emrsmsrli/WordClock/etc/img/backplate/1.jpg

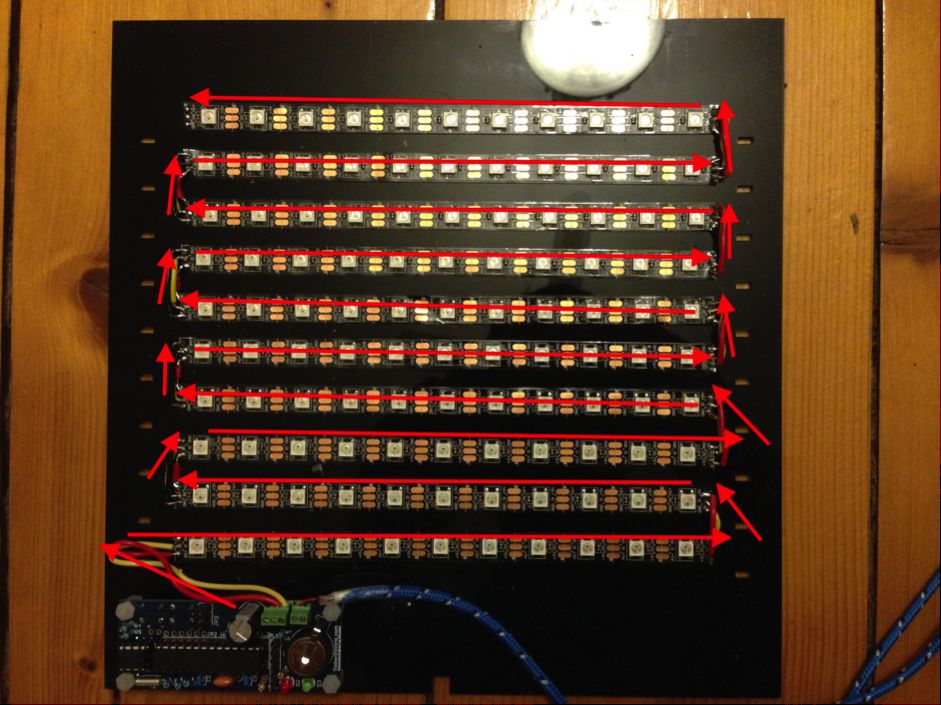
etc/img/backplate/1.jpg
