emrsmsrli/WordClock/etc/img/backplate/2.jpg

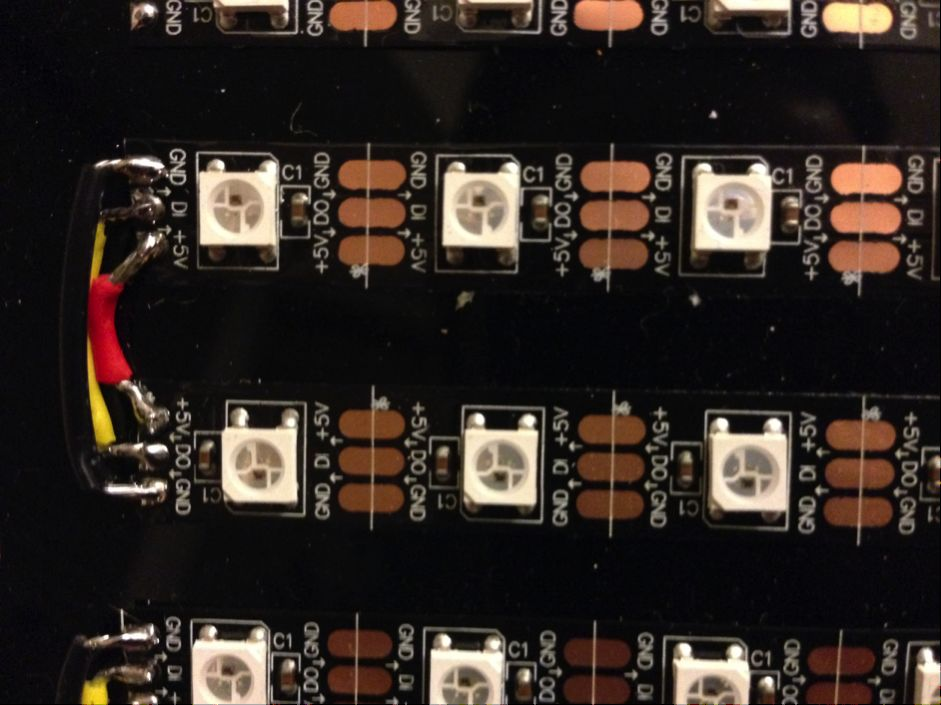
etc/img/backplate/2.jpg
