emrsmsrli/WordClock/etc/img/backplate/3.jpg

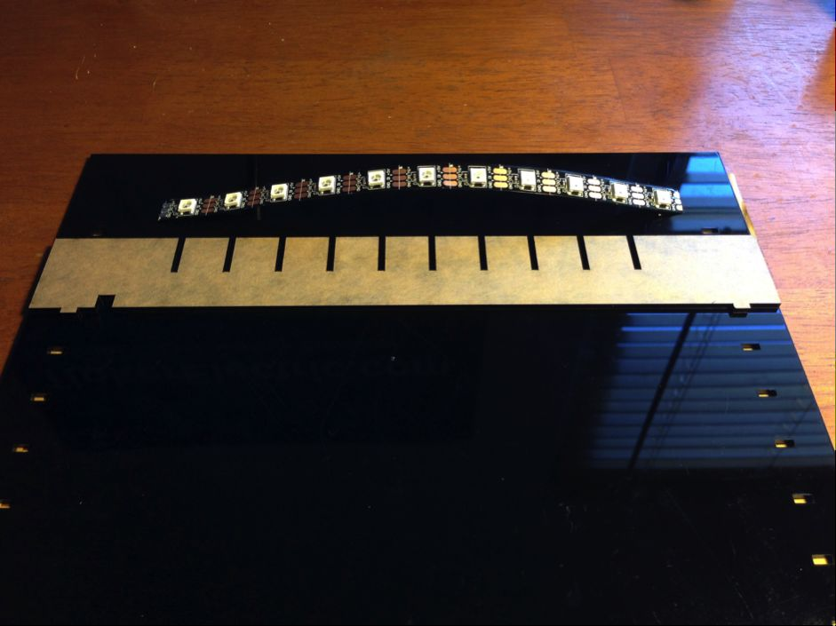
etc/img/backplate/3.jpg
