emrsmsrli/WordClock/etc/img/backplate/4.jpg

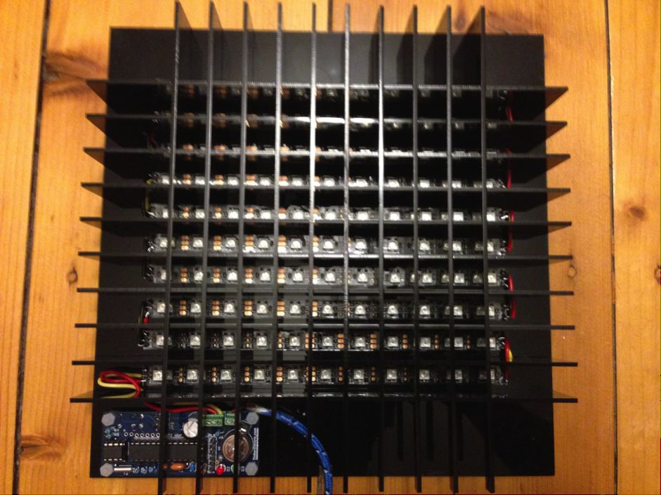
etc/img/backplate/4.jpg
