emrsmsrli/WordClock/etc/img/backplate/5.jpg

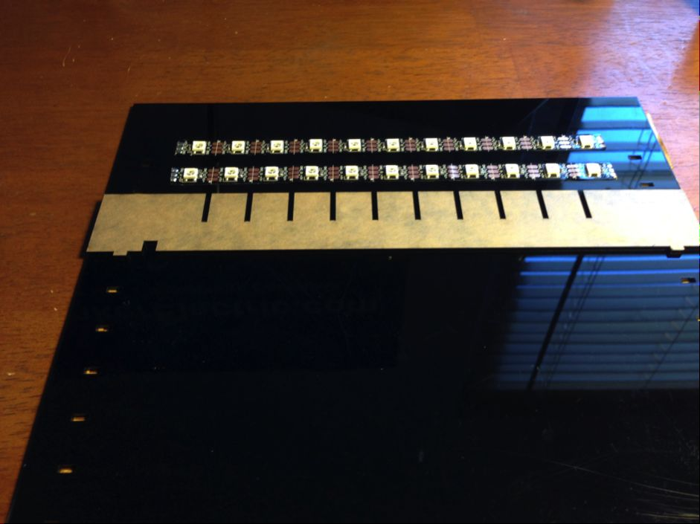
etc/img/backplate/5.jpg
