emrsmsrli/WordClock/etc/img/backplate/6.jpg

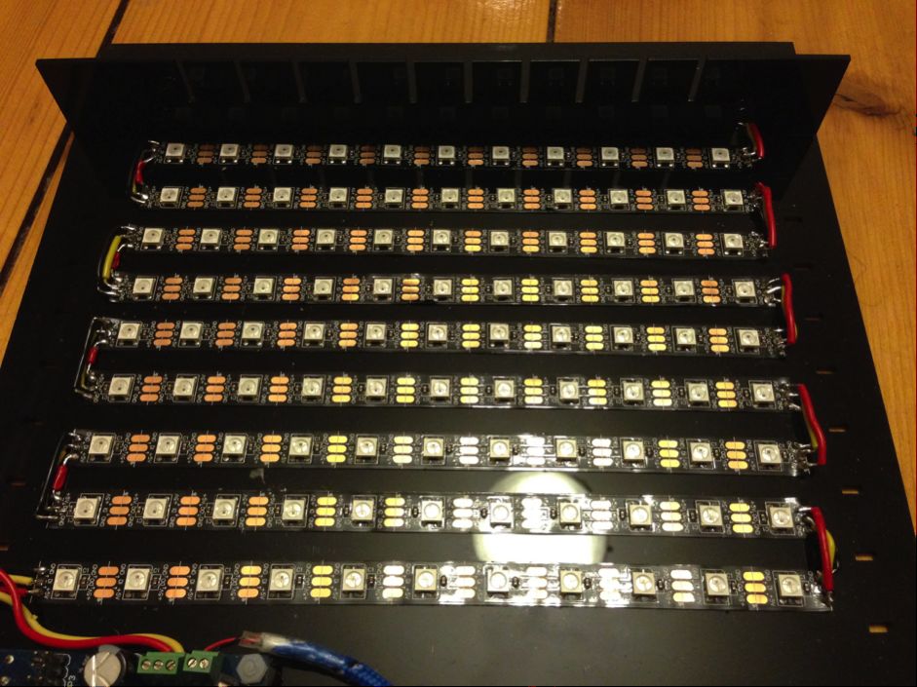
etc/img/backplate/6.jpg
