emrsmsrli/WordClock/etc/img/backplate/7.jpg

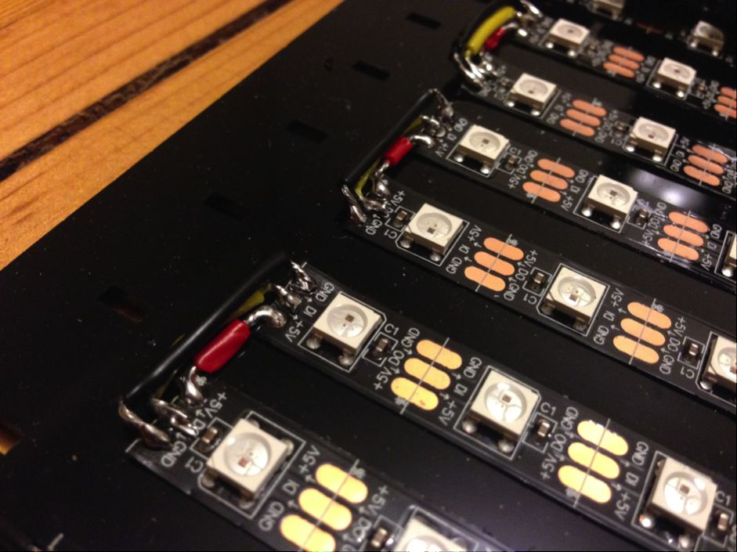
etc/img/backplate/7.jpg
