emrsmsrli/WordClock/etc/img/backplate/8.jpg

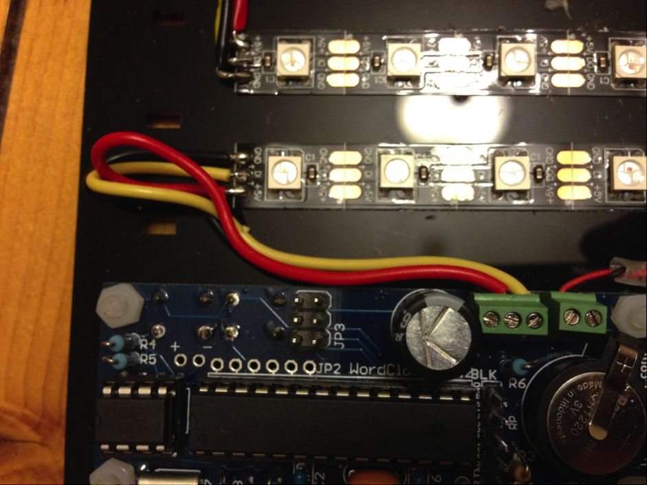
etc/img/backplate/8.jpg
