emrsmsrli/WordClock/etc/img/backplate/9.jpg

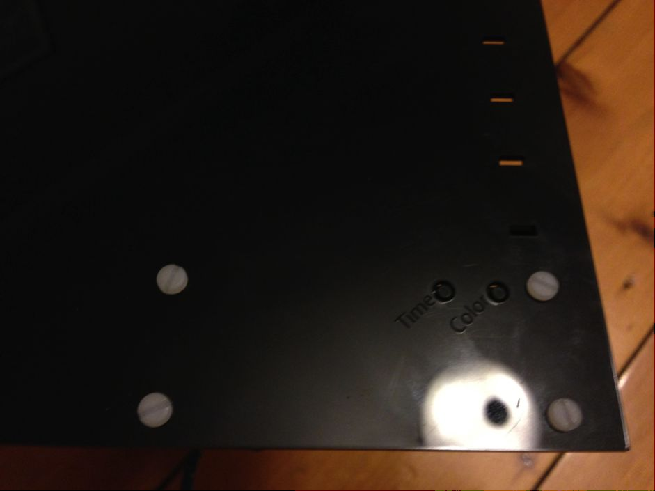
etc/img/backplate/9.jpg
