emrsmsrli/WordClock/etc/img/backplate/10.jpg

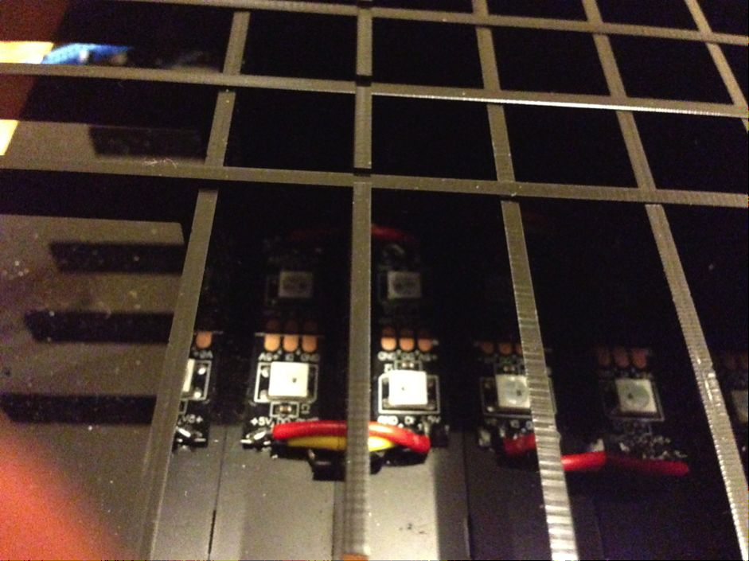
etc/img/backplate/10.jpg
