emrsmsrli/WordClock/etc/img/backplate/11.jpg

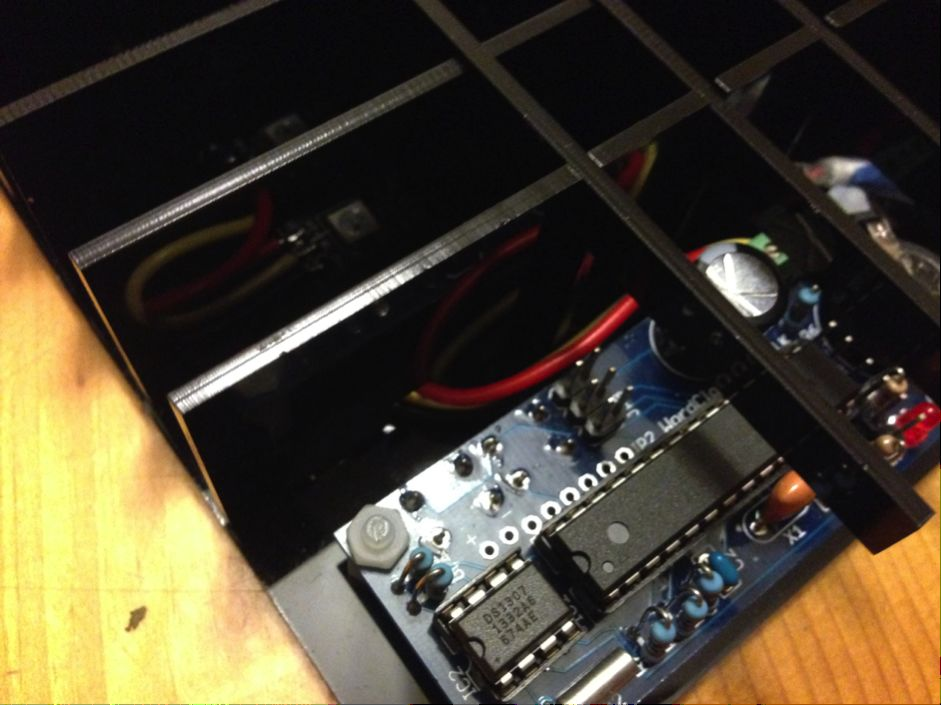
etc/img/backplate/11.jpg
