emrsmsrli/WordClock/etc/img/backplate/12.jpg

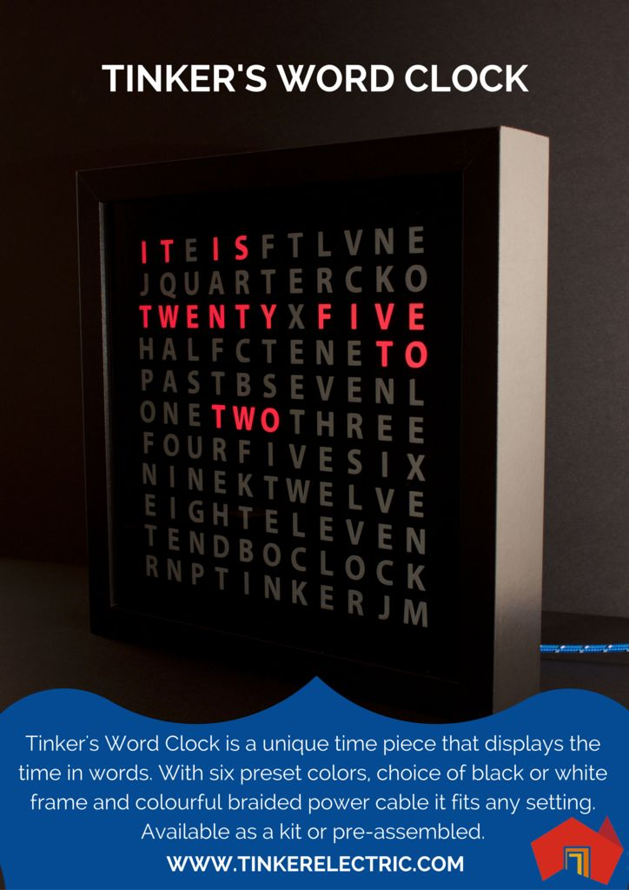
etc/img/backplate/12.jpg
