emrsmsrli/WordClock/etc/img/circuit/4.jpg

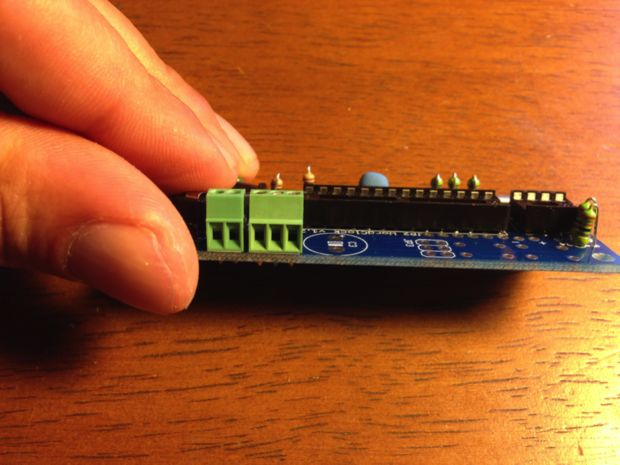
etc/img/circuit/4.jpg
