emrsmsrli/WordClock/etc/img/circuit/5.jpg

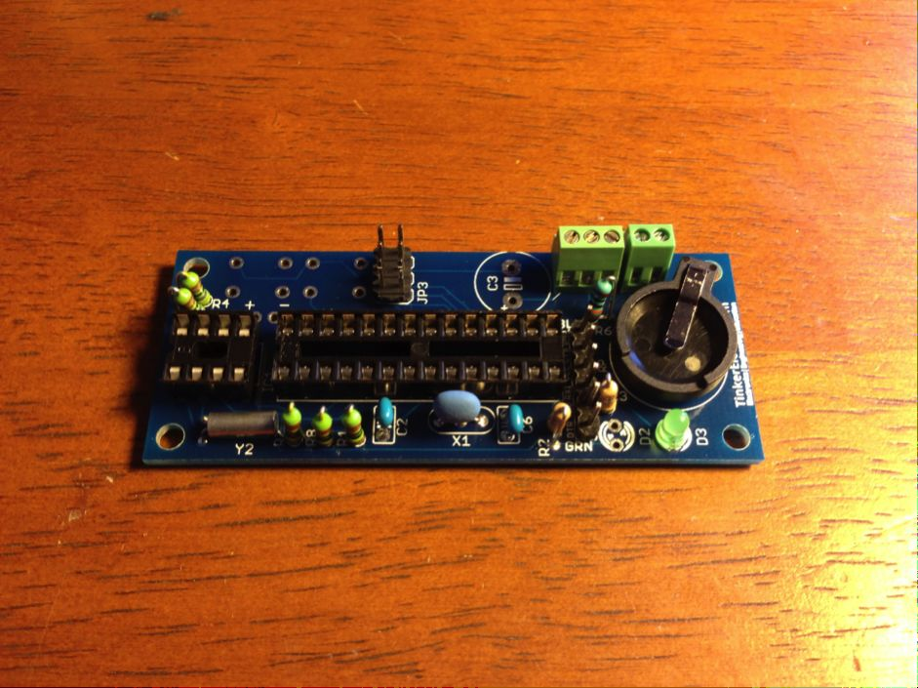
etc/img/circuit/5.jpg
