emrsmsrli/WordClock/etc/img/circuit/6.jpg

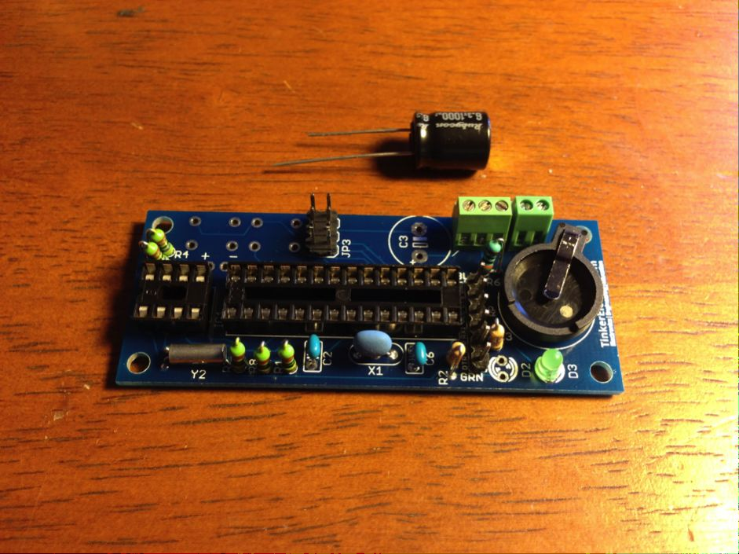
etc/img/circuit/6.jpg
