emrsmsrli/WordClock/etc/img/circuit/7.jpg

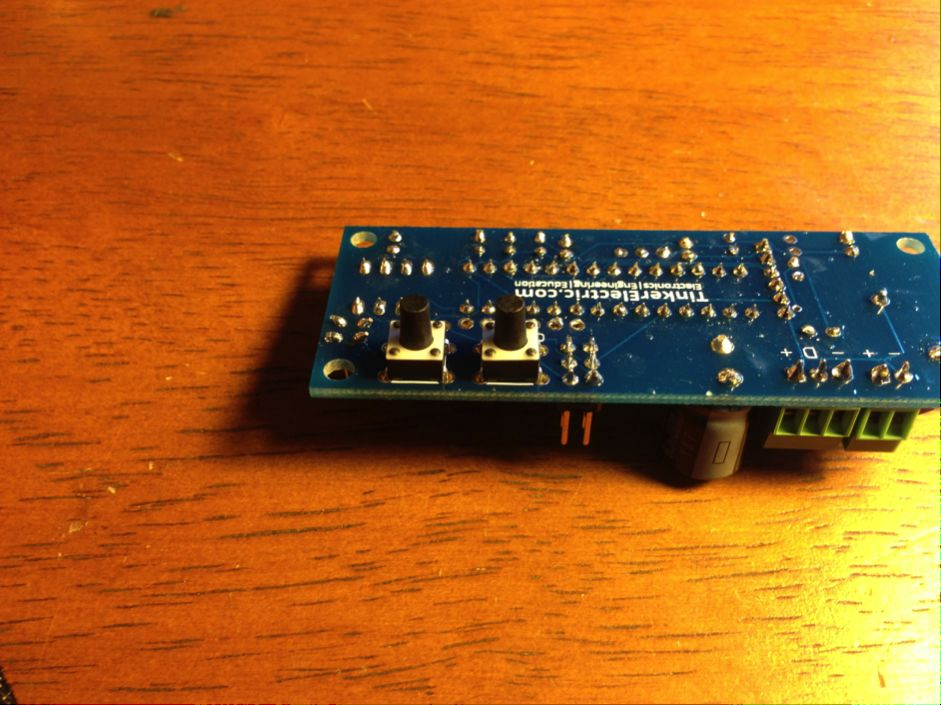
etc/img/circuit/7.jpg
