emrsmsrli/WordClock/etc/img/circuit/8.jpg

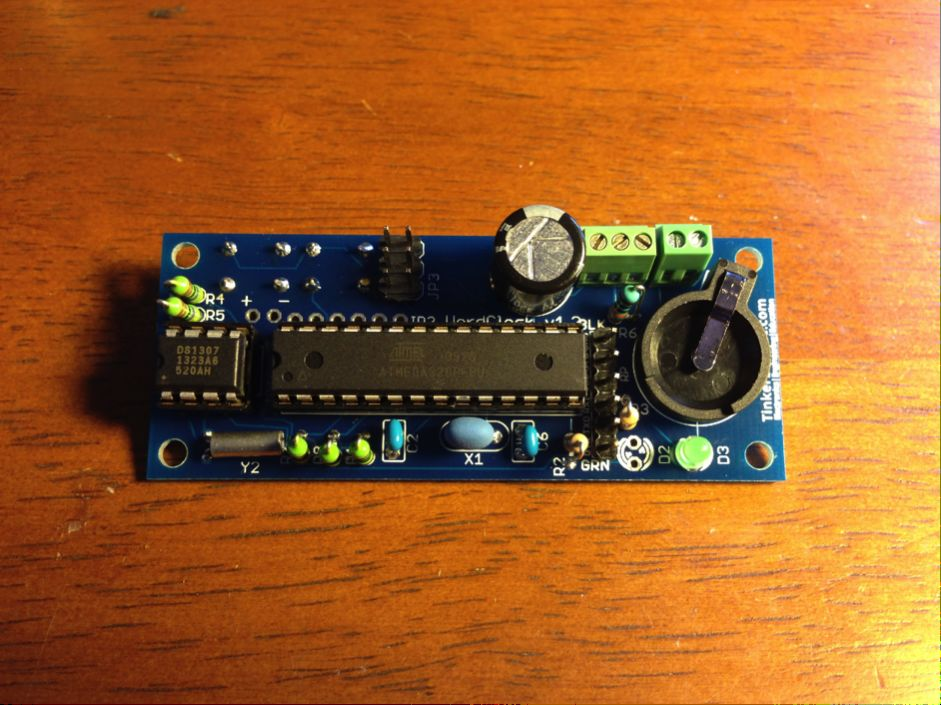
etc/img/circuit/8.jpg
