emrsmsrli/WordClock/etc/img/circuit/9.jpg

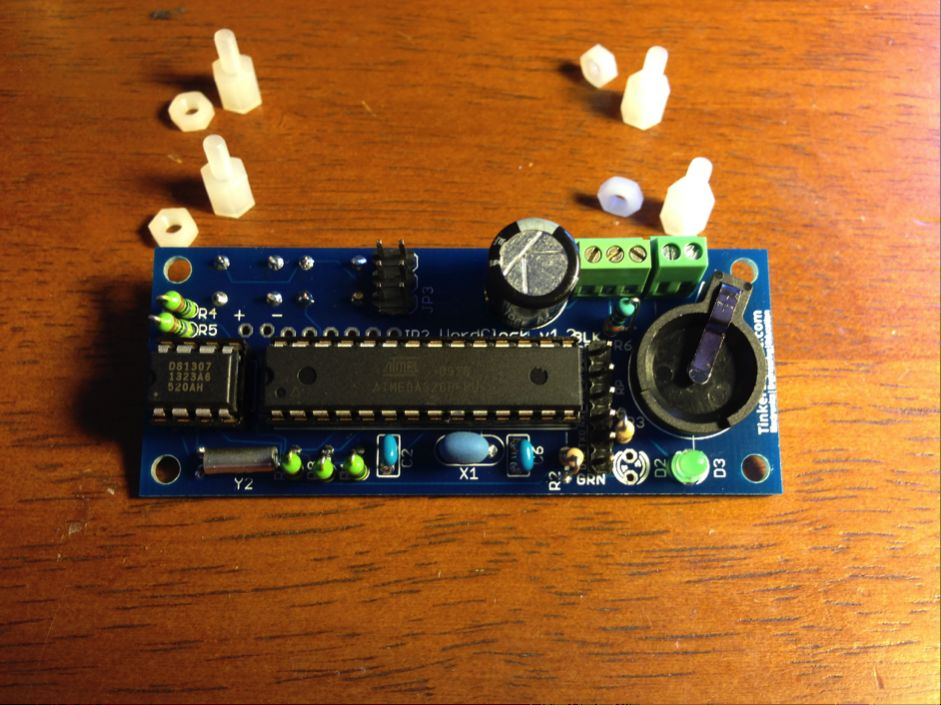
etc/img/circuit/9.jpg
