emrsmsrli/WordClock/etc/img/circuit/10.jpg

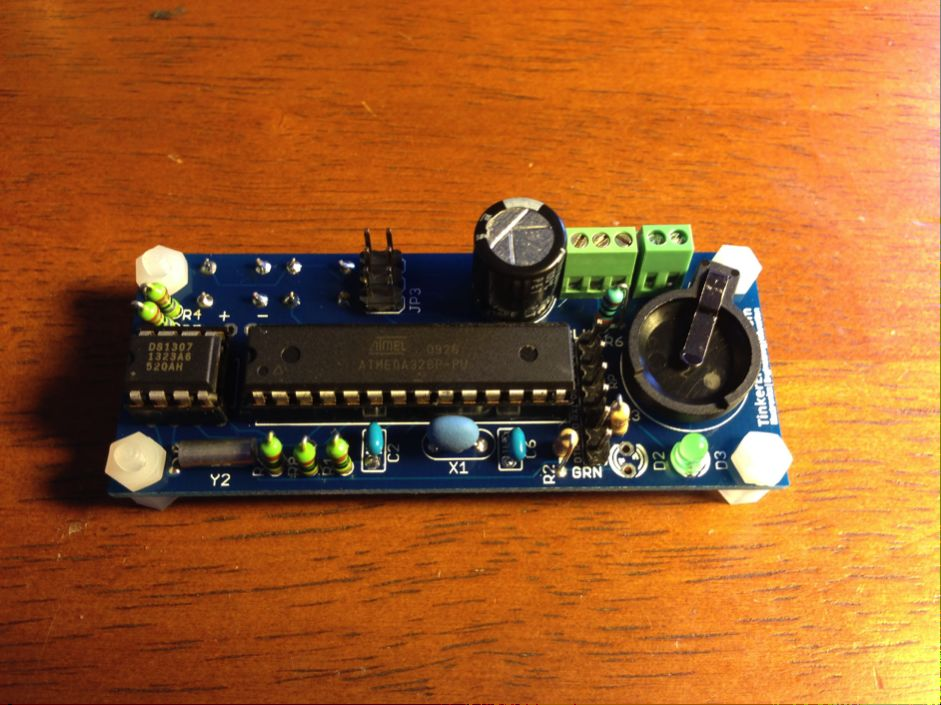
etc/img/circuit/10.jpg
