emrsmsrli/WordClock/etc/img/circuit/11.jpg

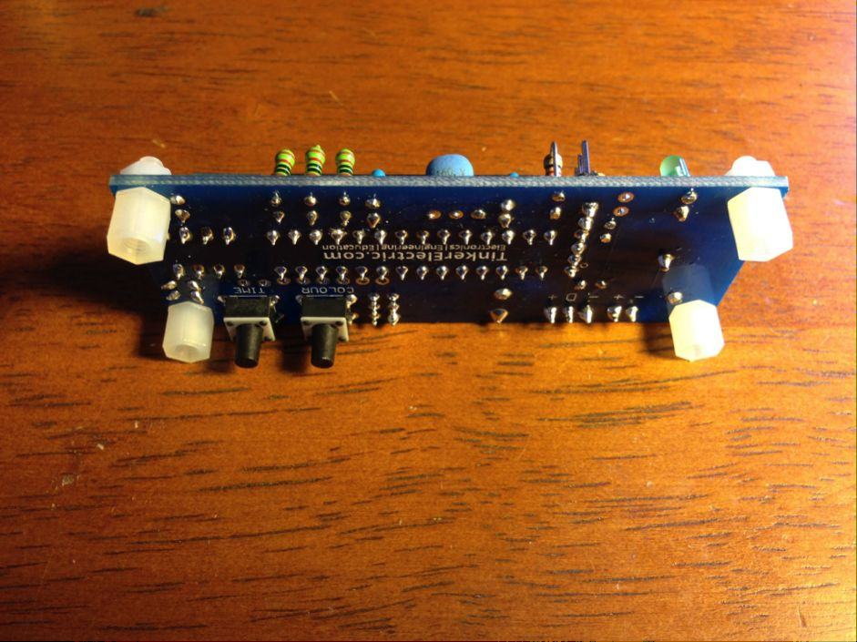
etc/img/circuit/11.jpg
