emrsmsrli/WordClock/etc/img/circuit/12.jpg

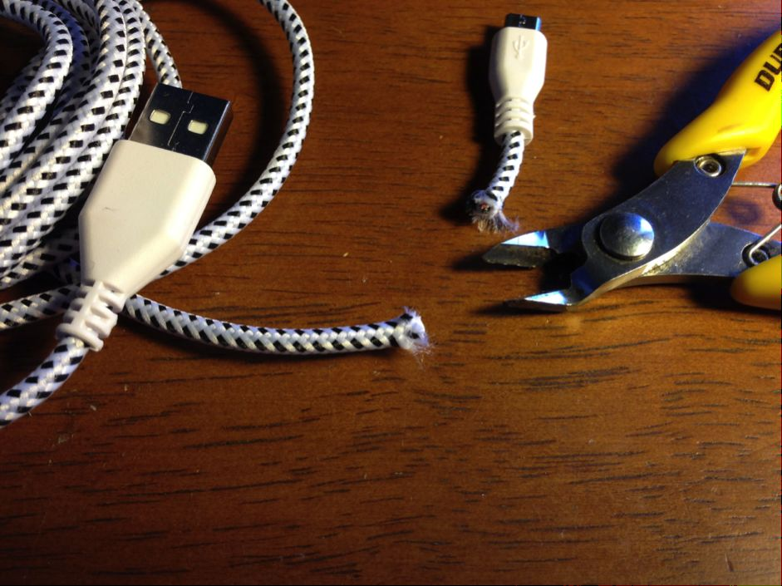
etc/img/circuit/12.jpg
