emrsmsrli/WordClock/etc/img/circuit/13.jpg

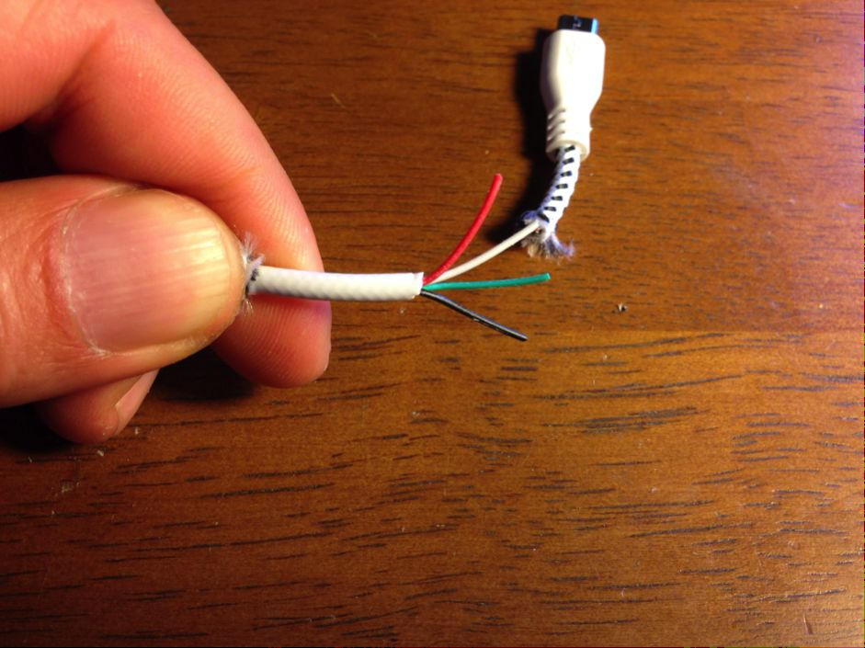
etc/img/circuit/13.jpg
