emrsmsrli/WordClock/etc/img/circuit/14.jpg

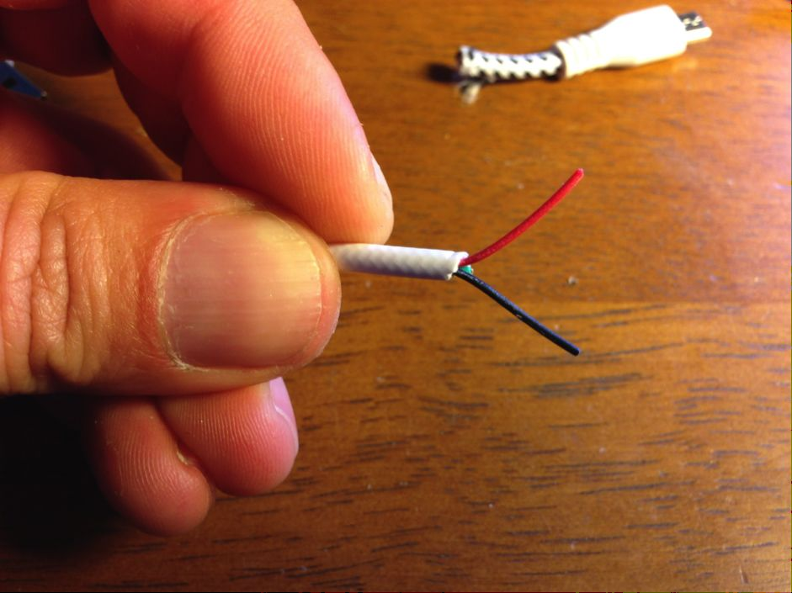
etc/img/circuit/14.jpg
