emrsmsrli/WordClock/etc/img/circuit/15.jpg

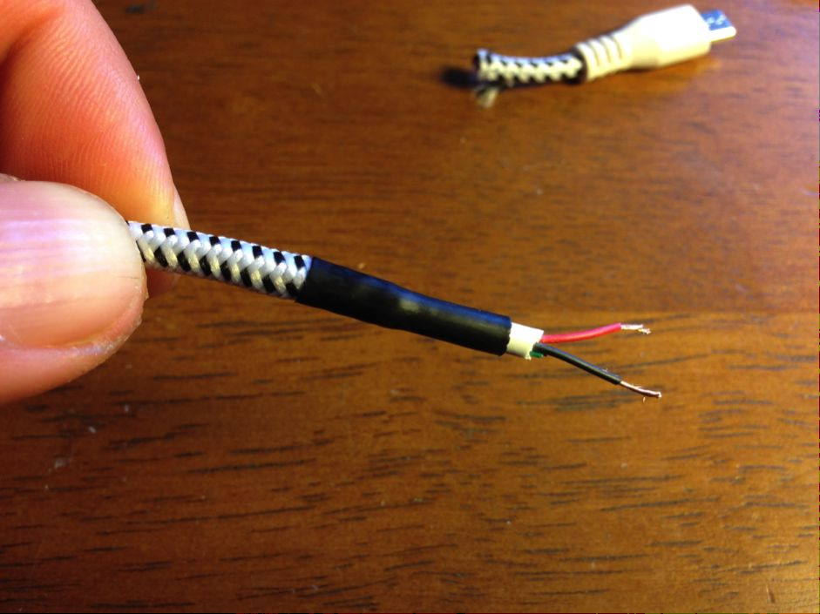
etc/img/circuit/15.jpg
