emrsmsrli/WordClock/etc/img/circuit/17.jpg

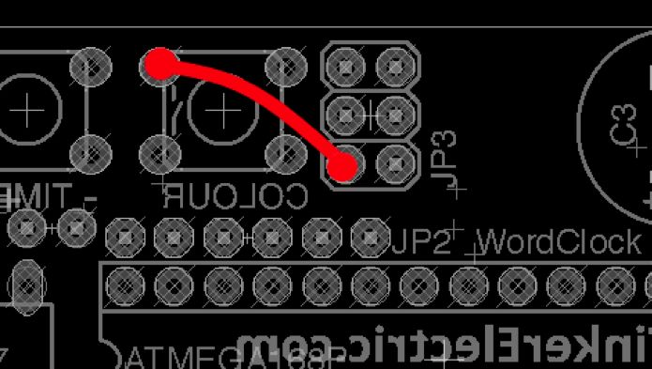
etc/img/circuit/17.jpg
