emrsmsrli/WordClock/etc/img/circuit/18.jpg

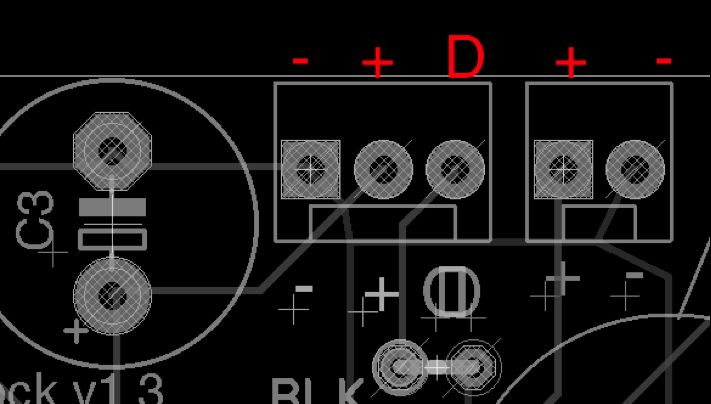
etc/img/circuit/18.jpg
